mattcaron/thermostat/sensors/main/config_storage.c

/**
 * @file
 * Functions to read and store our config.
 */
#include <string.h>
#include <stdlib.h>
#include "config_storage.h"
#include "nvs.h"

/* "backup_mac", "phy", and "dhcp_state" are all used by the system.
 * Ensure that this namespace declaration does not conflict with them
 * and is random enough so as to not conflict with anything which might
 * be used in the future.
 */
#define NVS_CONFIG_NAMESPACE "mc-sensorconfig"

#define NVS_SSID_NAME "ssid"
#define NVS_PASS_NAME "pass"
#define NVS_STATION_NAME "sta"
#define NVS_BITFIELD "bits"
#define NVS_POLL_TIME_SEC "poll"
#define NVS_URI "uri"
#define NVS_IP "ip"
#define NVS_NETMASK "nm"
#define NVS_GATEWAY "gw"
#define NVS_DNS "dns"

#define NVS_BITFIELD_USE_CELSIUS 0x00000001
#define NVS_BITFIELD_CACHE_AP    0x00000010
#define NVS_BITFIELD_USE_DHCP    0x00000100

// defaults
#define NVS_BITFIELD_DEFAULT (NVS_BITFIELD_USE_CELSIUS | NVS_BITFIELD_CACHE_AP)
#define POLL_TIME_DEFAULT_SEC 600

config_storage_t current_config;

config_storage_t new_config;

/**
 * Helper function to read a config string from NVS.
 *
 * @param handle [in]  handle to open NVS partition.
 * @param key    [in]  key whose value to retrieve.
 * @param value  [out] buffer to receive the value.
 * @param buflen [out] length of value, in bytes.
 *
 * @return an esp_err_t result as returned from nvs_get_str.
 */
static esp_err_t read_config_string_from_nvs(nvs_handle handle, const char *key,
        char *value, size_t buflen)
{
    // API docs say length includes NUL, so we don't want to subtract 1 in all
    // of these calculations.
    size_t length = buflen;
    esp_err_t ret = nvs_get_str(handle, key, value, &length);
    // It not being there is not an error - just ignore it and leave it blank.
    if (ret == ESP_ERR_NVS_NOT_FOUND) {
        ret = ESP_OK;
    }

    return ret;
}

/**
 * Helper function to read an IP from NVS.
 * 
 * @note This calls an ESP_ERR_CHECK and will throw an error for all errors that
 *       we don't handle.
 *
 * @param handle [in]  handle to open NVS partition.
 * @param key    [in]  key whose value to retrieve.
 * 
 * @return If found, the IP as read from NVS.
 * @return If not found, 0
 */
static uint32_t read_ip_from_nvs(nvs_handle handle, const char *key)
{
    esp_err_t ret;
    uint32_t temp_ip = 0;

    ret = nvs_get_u32(handle, key, &temp_ip);
    if (ret == ESP_ERR_NVS_NOT_FOUND) {
        temp_ip = 0;
        ret = ESP_OK;
    }
    // else the IP was either successfully retrieved or there is some other
    // error which we will test below.

    ESP_ERROR_CHECK(ret);

    return temp_ip;
}

bool read_config_from_nvs(config_storage_t *config)
{
    nvs_handle handle;
    esp_err_t ret;
    uint32_t bitfield;

    // zero our structure.
    memset(config, 0, sizeof(config_storage_t));

    ret = nvs_open(NVS_CONFIG_NAMESPACE, NVS_READONLY, &handle);
    if (ret == ESP_ERR_NVS_NOT_FOUND) {
        /* The first time we open this, it can fail if the namespace doesn't
         * exist. It would create it, except we opened it read only. So, open it
         * read write, just once. But, since it is newly created, we can skip
         * the rest of the logic, since we haven't stored anything yet. Since we
         * zero the config structure above, very little further work is
         * necessary, just an open and close.
         */
        ESP_ERROR_CHECK(nvs_open(NVS_CONFIG_NAMESPACE, NVS_READWRITE, &handle));

        // One thing we do have to do is set the default polling interval,
        // otherwise it will go nuts polling until the WDT resets it.
        config->poll_time_sec = POLL_TIME_DEFAULT_SEC;
    }
    else {
        // Catch any other errors not related to it not being there.
        ESP_ERROR_CHECK(ret);

        // Read out the rest of our config items.
        ESP_ERROR_CHECK(read_config_string_from_nvs(handle, NVS_SSID_NAME,
                        config->ssid, sizeof(config->ssid)));
        ESP_ERROR_CHECK(read_config_string_from_nvs(handle, NVS_PASS_NAME,
                        config->pass, sizeof(config->pass)));
        ESP_ERROR_CHECK(read_config_string_from_nvs(handle, NVS_STATION_NAME,
                        config->station_name, sizeof(config->station_name)));

        ret = nvs_get_u32(handle, NVS_BITFIELD, &bitfield);
        if (ret == ESP_ERR_NVS_NOT_FOUND) {
            bitfield = NVS_BITFIELD_DEFAULT;
            ret = ESP_OK;
        }
        ESP_ERROR_CHECK(ret);

        // Decode all bitfield items
        if (bitfield & NVS_BITFIELD_USE_CELSIUS) {
            config->use_celsius = true;
        }
        else {
            config->use_celsius = false;
        }

        if (bitfield & NVS_BITFIELD_CACHE_AP) {
            config->cache_ap_info = true;
        }
        else {
            config->cache_ap_info = false;
        }

        if (bitfield & NVS_BITFIELD_USE_DHCP) {
            config->use_dhcp = true;
        }
        else {
            config->use_dhcp = false;
        }

        ret = nvs_get_u16(handle, NVS_POLL_TIME_SEC, &config->poll_time_sec);
        if (ret == ESP_ERR_NVS_NOT_FOUND) {
            config->poll_time_sec = POLL_TIME_DEFAULT_SEC;
            ret = ESP_OK;
        }
        ESP_ERROR_CHECK(ret);

        ESP_ERROR_CHECK(read_config_string_from_nvs(handle, NVS_URI,
            config->uri, sizeof(config->uri)));

        // these following 4 IPs will be ignored if use_dhcp is false
        
        config->ipaddr.addr = read_ip_from_nvs(handle, NVS_IP);
        config->netmask.addr = read_ip_from_nvs(handle, NVS_NETMASK);
        config->gateway.addr = read_ip_from_nvs(handle, NVS_GATEWAY);
        config->dns.addr = read_ip_from_nvs(handle, NVS_DNS);
    }

    nvs_close(handle);

    return true;
}

bool write_config_to_nvs(config_storage_t *config)
{
    nvs_handle handle;
    uint32_t bitfield = 0;

    ESP_ERROR_CHECK(nvs_open(NVS_CONFIG_NAMESPACE, NVS_READWRITE, &handle));

    if (config->use_celsius) {
        bitfield |= NVS_BITFIELD_USE_CELSIUS;
    }
    else {
        bitfield &= ~NVS_BITFIELD_USE_CELSIUS;
    }

    if (config->cache_ap_info) {
        bitfield |= NVS_BITFIELD_CACHE_AP;
    }
    else {
        bitfield &= ~NVS_BITFIELD_CACHE_AP;
    }

    if (config->use_dhcp) {
        bitfield |= NVS_BITFIELD_USE_DHCP;
    }
    else {
        bitfield &= ~NVS_BITFIELD_USE_DHCP;
    }    

    // Write out our config items.
    ESP_ERROR_CHECK(nvs_set_str(handle, NVS_SSID_NAME,
                                config->ssid));
    ESP_ERROR_CHECK(nvs_set_str(handle, NVS_PASS_NAME,
                                config->pass));
    ESP_ERROR_CHECK(nvs_set_str(handle, NVS_STATION_NAME,
                                config->station_name));
    ESP_ERROR_CHECK(nvs_set_u32(handle, NVS_BITFIELD, bitfield))
    ESP_ERROR_CHECK(nvs_set_u16(handle, NVS_POLL_TIME_SEC,
                                config->poll_time_sec));
    ESP_ERROR_CHECK(nvs_set_str(handle, NVS_URI,
                                config->uri));
    ESP_ERROR_CHECK(nvs_set_u32(handle, NVS_IP, config->ipaddr.addr));
    ESP_ERROR_CHECK(nvs_set_u32(handle, NVS_NETMASK, config->netmask.addr));
    ESP_ERROR_CHECK(nvs_set_u32(handle, NVS_GATEWAY, config->gateway.addr));
    ESP_ERROR_CHECK(nvs_set_u32(handle, NVS_DNS, config->dns.addr));

    nvs_commit(handle);

    nvs_close(handle);

    return true;
}

bool is_config_valid(config_storage_t *config)
{
    // this is somewhat optimized for efficiency by using multiple returns, in
    // violation of best practices.

    if (strlen(config->ssid) == 0) {
        return false;
    }

    if (strlen(config->pass) == 0) {
        return false;
    }

    // cache_ap_info has 2 states, both valid

    // use_dhcp has 2 states, both valid, but if we are not using DHCP, we need
    // to check other things.
    if (!config->use_dhcp) {
        // rudimentary validity check, just make sure it's nonzero.
        if (config->ipaddr.addr == 0) {
                return false;
        }

        if (ip4_addr_netmask_valid(config->netmask.addr) == 0) {
            return false;
        }
        
        // we don't check gateway or dns because they're not strictly necessary,
        // so people can leave them blank if they won't ever use them.
    }

    if (strlen(config->station_name) == 0) {
        return false;
    }

    // use_celsius only has 2 states, both valid

    // The minimum is 1 second. The maximum is UINT16_MAX, which this can never
    // be more than, so we don't need to test for.
    if (config->poll_time_sec < 1) {
        return false;
    }

    if (strlen(config->uri) == 0) {
        return false;
    }

    return true;
}
