mattcaron/thermostat/sensors/main/cmd_system.c

/**
 * @file
 * Various system console commands.
 *
 * Derived from ESP8266_RTOS_SDK example
 * examples/system/console/components/cmd_system/cmd_system.c, which
 * is licensed as Public Domain.
 */

#include <stdio.h>
#include <string.h>
#include <ctype.h>
#include "esp_log.h"
#include "esp_attr.h"
#include "esp_console.h"
#include "esp_system.h"
#include "esp_sleep.h"
#include "esp_spi_flash.h"
#include "argtable3/argtable3.h"
#include "freertos/FreeRTOS.h"
#include "freertos/task.h"
#include "temperature.h"
#include "version.h"

#ifdef CONFIG_FREERTOS_USE_STATS_FORMATTING_FUNCTIONS
#define WITH_TASKS_INFO 1
#endif

static const char *TAG = "cmd_system";

static void register_free(void);
static void register_heap(void);
static void register_version(void);
static void register_restart(void);
static void register_tasks(void);
static void register_nosleep(void);
static void register_pause(void);

void register_system(void)
{
    register_free();
    register_heap();
    register_version();
    register_restart();
    register_tasks();
    register_nosleep();
    register_pause();
}

/* 'version' command */
static int get_version(int argc, char **argv)
{
    esp_chip_info_t info;
    esp_chip_info(&info);
    printf("IDF Version:%s\r\n", esp_get_idf_version());
    printf("Chip info:\r\n");
    printf("\tmodel:%s\r\n", info.model == CHIP_ESP8266 ? "ESP8266" : "Unknow");
    printf("\tcores:%d\r\n", info.cores);
    printf("\tfeature:%s%s%s%s%d%s\r\n",
           info.features & CHIP_FEATURE_WIFI_BGN ? "/802.11bgn" : "",
           info.features & CHIP_FEATURE_BLE ? "/BLE" : "",
           info.features & CHIP_FEATURE_BT ? "/BT" : "",
           info.features & CHIP_FEATURE_EMB_FLASH ? "/Embedded-Flash:" :
           "/External-Flash:",
           spi_flash_get_chip_size() / (1024 * 1024), " MB");
    printf("\trevision number:%d\r\n", info.revision);
    printf("\nSoftware version %d.%d.%d\n", SW_MAJOR, SW_MINOR, SW_PATCH);
    return 0;
}

static void register_version(void)
{
    const esp_console_cmd_t cmd = {
        .command = "version",
        .help = "Get version of chip and SDK",
        .hint = NULL,
        .func = &get_version,
    };
    ESP_ERROR_CHECK( esp_console_cmd_register(&cmd) );
}

/** 'restart' command restarts the program */

static int restart(int argc, char **argv)
{
    printf("Restarting");
    esp_restart();
}

static void register_restart(void)
{
    const esp_console_cmd_t cmd = {
        .command = "restart",
        .help = "Software reset of the chip",
        .hint = NULL,
        .func = &restart,
    };
    ESP_ERROR_CHECK( esp_console_cmd_register(&cmd) );
}

/** 'free' command prints available heap memory */

static int free_mem(int argc, char **argv)
{
    printf("%d\n", esp_get_free_heap_size());
    return 0;
}

static void register_free(void)
{
    const esp_console_cmd_t cmd = {
        .command = "free",
        .help = "Get the current size of free heap memory",
        .hint = NULL,
        .func = &free_mem,
    };
    ESP_ERROR_CHECK( esp_console_cmd_register(&cmd) );
}

/* 'heap' command prints minumum heap size */
static int heap_size(int argc, char **argv)
{
    uint32_t heap_size = heap_caps_get_minimum_free_size(MALLOC_CAP_32BIT);
    printf("min heap size: %u\n", heap_size);
    return 0;
}

static void register_heap(void)
{
    const esp_console_cmd_t heap_cmd = {
        .command = "heap",
        .help = "Get minimum size of free heap memory that was available during program execution",
        .hint = NULL,
        .func = &heap_size,
    };
    ESP_ERROR_CHECK( esp_console_cmd_register(&heap_cmd) );

}

static int tasks_info(int argc, char **argv)
{
    const size_t bytes_per_task = 40; /* see vTaskList description */
    char *task_list_buffer = malloc(uxTaskGetNumberOfTasks() * bytes_per_task);
    if (task_list_buffer == NULL) {
        ESP_LOGE(TAG, "failed to allocate buffer for vTaskList output");
        return 1;
    }
    fputs("Task Name\tStatus\tPrio\tHWM\tTask#", stdout);
#ifdef CONFIG_FREERTOS_VTASKLIST_INCLUDE_COREID
    fputs("\tAffinity", stdout);
#endif
    fputs("\n", stdout);
    vTaskList(task_list_buffer);
    fputs(task_list_buffer, stdout);
    free(task_list_buffer);
    return 0;
}

static void register_tasks(void)
{
    const esp_console_cmd_t cmd = {
        .command = "tasks",
        .help = "Get information about running tasks",
        .hint = NULL,
        .func = &tasks_info,
    };
    ESP_ERROR_CHECK(esp_console_cmd_register(&cmd));
}

static int disable_sleep(int argc, char **argv)
{
    disable_deep_sleep();
    printf("Deep sleep disabled.\n");
    printf("Perform any needed configuration, then issue a `restart` \n"
           "command to re-enable deep sleep.\n");
    return 0;
}

static int pause(int argc, char **argv)
{
    enable_pause();
    printf("Temperature processing and sleeping paused.\n");
    printf("Perform any needed configuration, then issue a `restart` command.\n");
    return 0;
}

static void register_nosleep(void)
{
    const esp_console_cmd_t cmd = {
        .command = "nosleep",
        .help = "Disable sleep mode",
        .hint = NULL,
        .func = &disable_sleep,
    };
    ESP_ERROR_CHECK(esp_console_cmd_register(&cmd));
}

static void register_pause(void)
{
    const esp_console_cmd_t cmd = {
        .command = "pause",
        .help = "Disable temperature sending",
        .hint = NULL,
        .func = &pause,
    };
    ESP_ERROR_CHECK(esp_console_cmd_register(&cmd));
}
