mattcaron/thermostat/sensors/main/version.h

/**
 * @file
 * Version information.
 */

#ifndef __VERSION_H_
#define __VERSION_H_

// Standard SEMVER versioning. See https://semver.org/.
#define SW_MAJOR 1
#define SW_MINOR 0
#define SW_PATCH 0

#endif // __VERSION_H_
