mattcaron/thermostat/sensors/main/console.h

/**
 * @file
 * Header file for console.c.
 */

#ifndef __CONSOLE_H_
#define __CONSOLE_H_

/**
 * Start the console task.
 */
void start_console(void);

/**
 * Set the console prompt text.
 */
void set_console_prompt_text(void);

#endif // __CONSOLE_H_
