mattcaron/thermostat/sensors/main/cmd_config.h

/**
 * @file
 * Header for cmd_config.c.
 */

#ifndef __CMD_CONFIG_H_
#define __CMD_CONFIG_H_

/**
 * Register all configuration-related commands.
 */
void register_configure(void);

#endif // __CMD_CONFIG_H_
